Mihax209/mispecky/media/mispecky box 2.jpeg

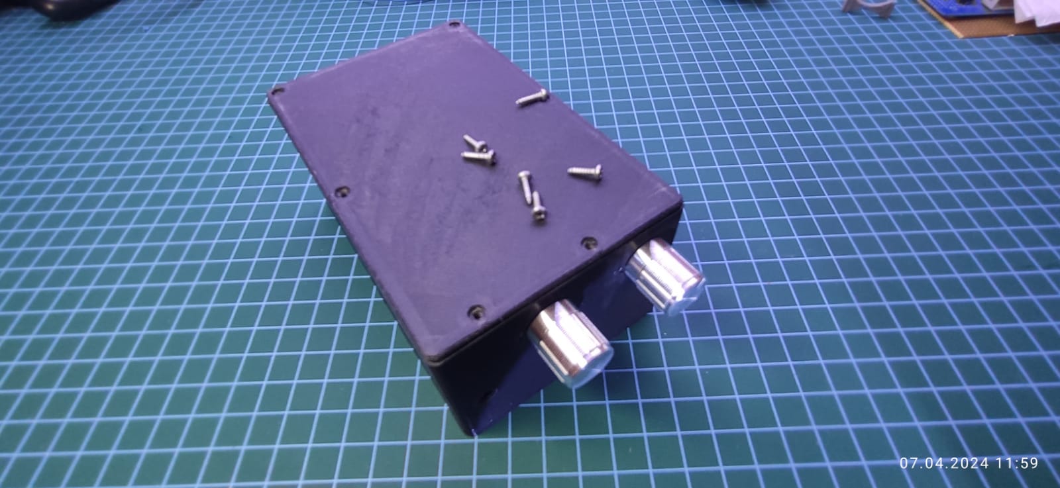
media/mispecky box 2.jpeg
