Mihax209/mispecky/src/models/Meshify C TG/partial stl/Meshify FULLcache_psu_001.stl

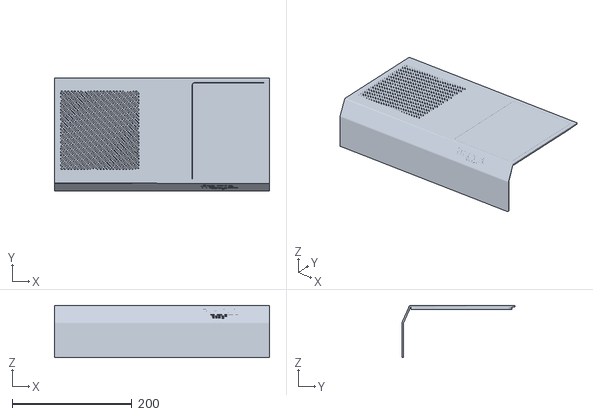
[picture p21: CAD file, 2024-03-31]
src/models/Meshify C TG/partial stl/Meshify FULLcache_psu_001.stl
359.7 x 189.7 x 87.1
