Mihax209/mispecky/models/Meshify C TG/full stl/Meshify BodyPieds_tour.stl

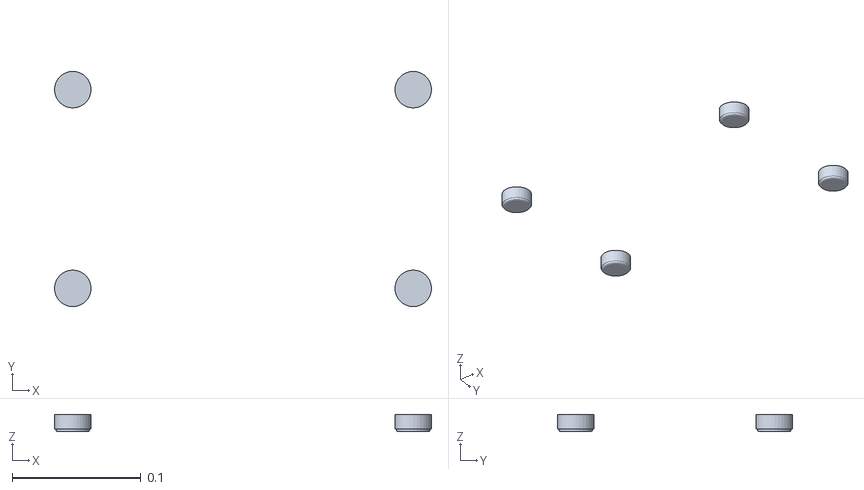
[picture p22: CAD file, 2024-03-31]
models/Meshify C TG/full stl/Meshify BodyPieds_tour.stl
0.293 x 0.183 x 0.0134
