Mihax209/mispecky/src/models/Meshify C TG/full stl/Meshify BodySupport_motherboard_002.stl

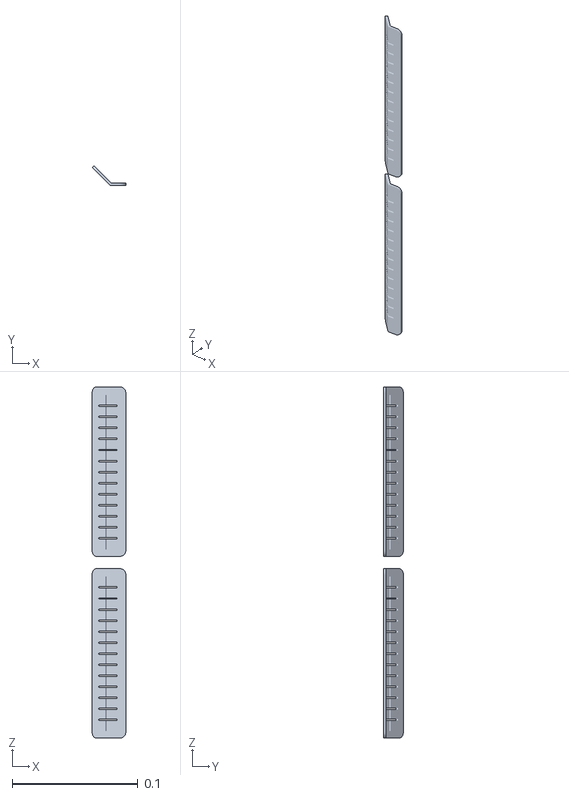
[picture p23: CAD file, 2024-03-31]
src/models/Meshify C TG/full stl/Meshify BodySupport_motherboard_002.stl
0.0268 x 0.0157 x 0.279
