Mihax209/mispecky/models/Meshify C TG/full stl/Meshify BodyHaut.stl

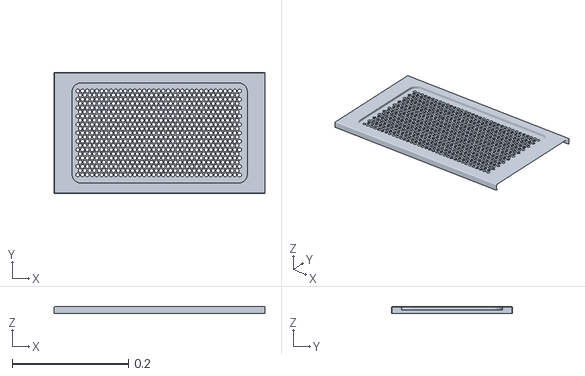
[picture p24: CAD file, 2024-03-31]
models/Meshify C TG/full stl/Meshify BodyHaut.stl
0.363 x 0.208 x 0.0118
