Mihax209/mispecky/src/models/Meshify C TG/full stl/Meshify Bodycaoutchouc_vitre_002.stl

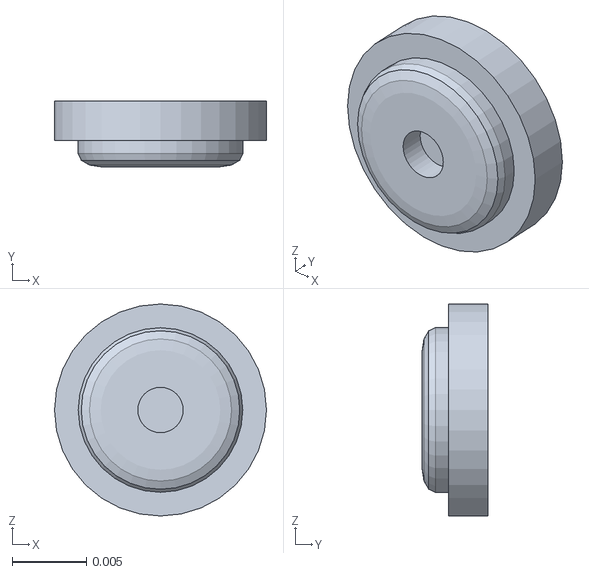
[picture p25: CAD file, 2024-03-31]
src/models/Meshify C TG/full stl/Meshify Bodycaoutchouc_vitre_002.stl
0.0143 x 0.00442 x 0.0143
