Mihax209/mispecky/models/Meshify C TG/full stl/Meshify Bodygrille_sup.stl

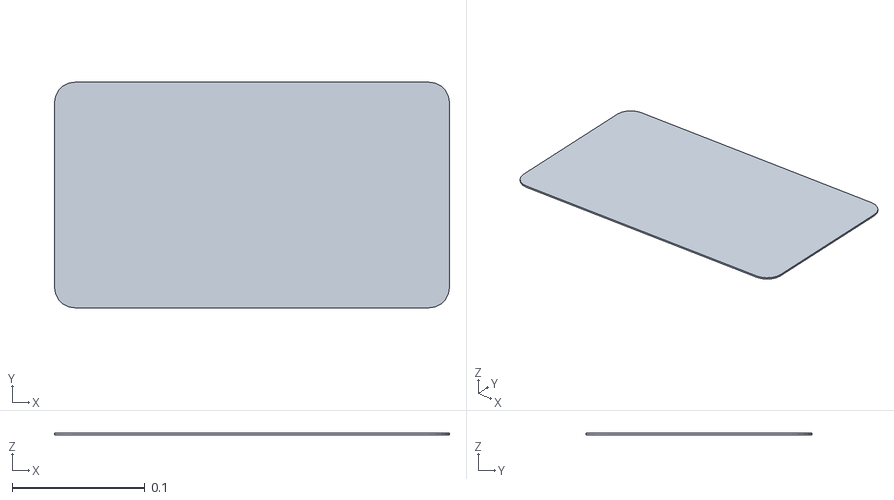
[picture p26: CAD file, 2024-03-31]
models/Meshify C TG/full stl/Meshify Bodygrille_sup.stl
0.298 x 0.17 x 0.00142
