Mihax209/mispecky/models/Meshify C TG/full stl/Meshify BodyLogo_front.stl

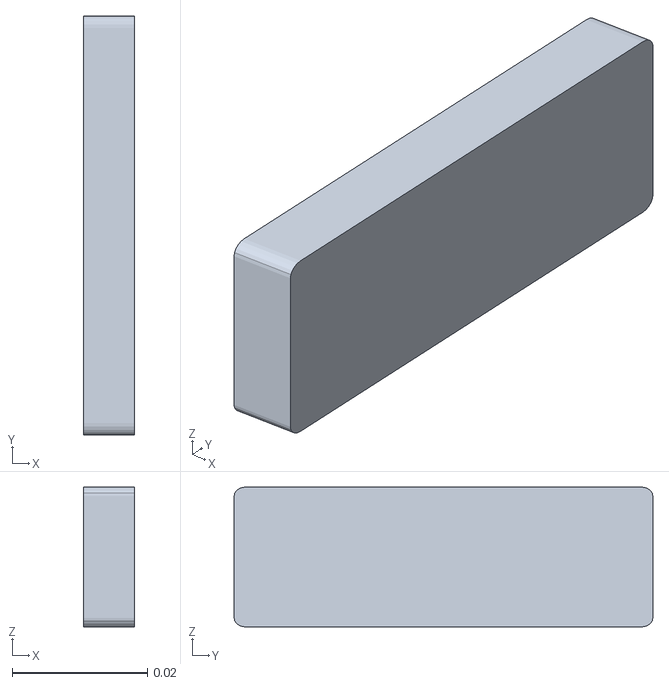
[picture p27: CAD file, 2024-03-31]
models/Meshify C TG/full stl/Meshify BodyLogo_front.stl
0.00752 x 0.0619 x 0.0207
