Mihax209/mispecky/src/models/Meshify C TG/full stl/Meshify Bodycache_psu_001.stl

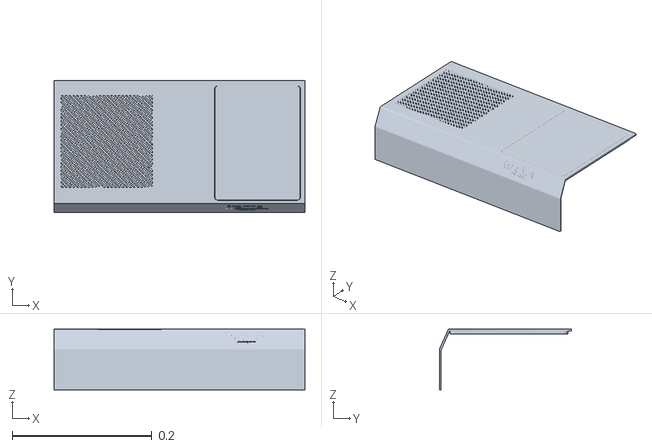
[picture p28: CAD file, 2024-03-31]
src/models/Meshify C TG/full stl/Meshify Bodycache_psu_001.stl
0.36 x 0.19 x 0.0871
