Mihax209/mispecky/models/Meshify C TG/full stl/Meshify BodyBas.stl

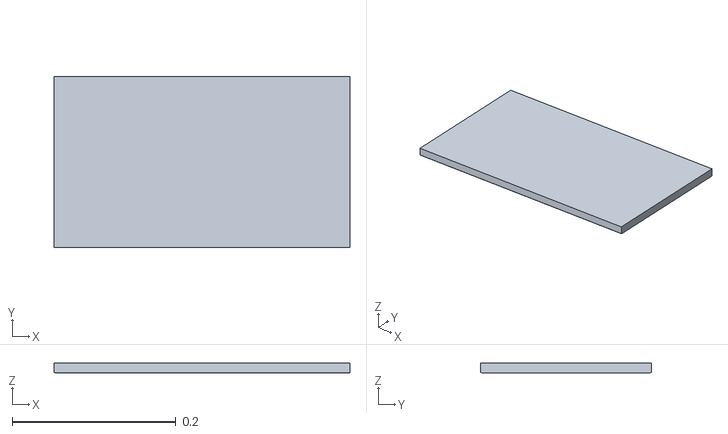
[picture p29: CAD file, 2024-03-31]
models/Meshify C TG/full stl/Meshify BodyBas.stl
0.361 x 0.208 x 0.0117
