Mihax209/mispecky/src/models/Meshify C TG/full stl/Meshify Bodyslot_plates.stl

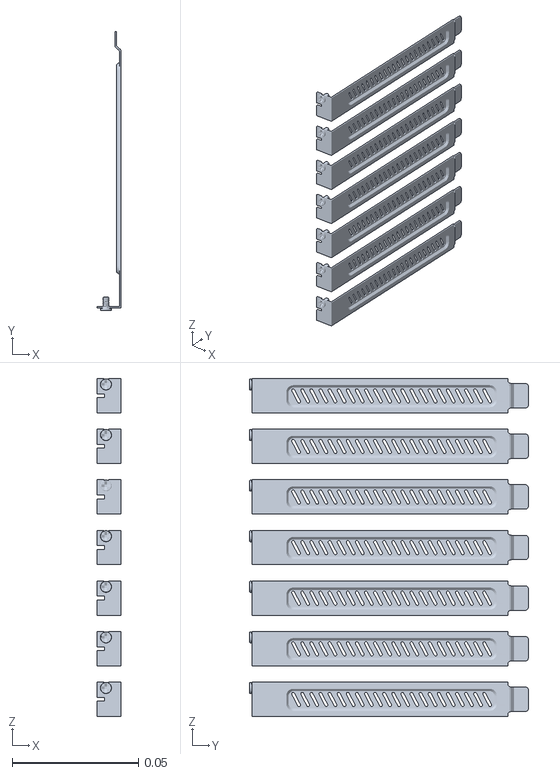
[picture p30: CAD file, 2024-03-31]
src/models/Meshify C TG/full stl/Meshify Bodyslot_plates.stl
0.00951 x 0.11 x 0.134
