Mihax209/mispecky/src/models/Meshify C TG/full stl/Meshify Bodyvis_TG.stl

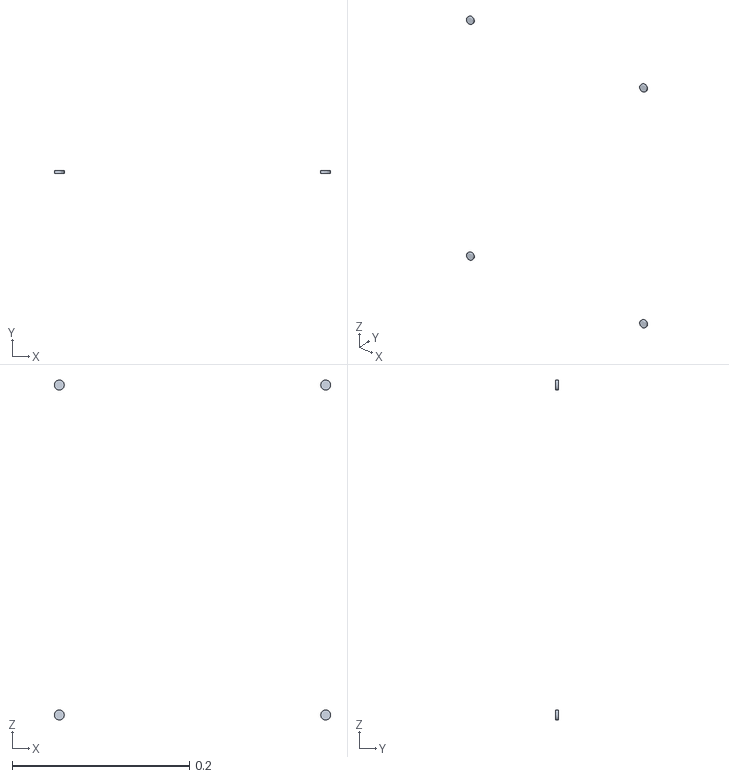
[picture p31: CAD file, 2024-03-31]
src/models/Meshify C TG/full stl/Meshify Bodyvis_TG.stl
0.312 x 0.00378 x 0.384
