Mihax209/mispecky/models/Meshify C TG/full stl/Meshify BodyFront_panel_002.stl

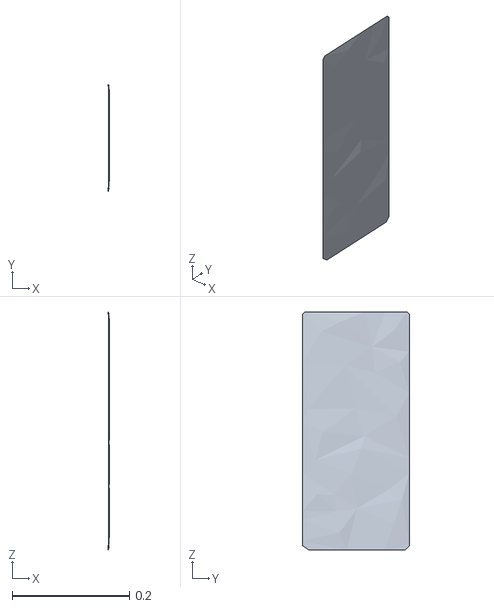
[picture p32: CAD file, 2024-03-31]
models/Meshify C TG/full stl/Meshify BodyFront_panel_002.stl
0.00219 x 0.183 x 0.407
