Mihax209/mispecky/src/models/Meshify C TG/full stl/Meshify BodyGrande_vis_002.stl

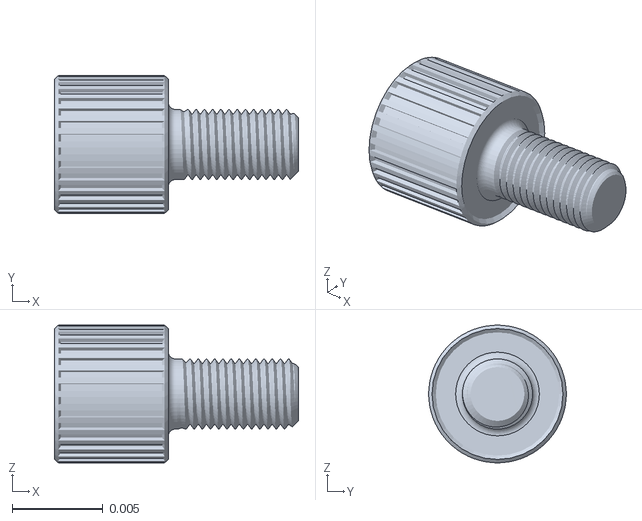
[picture p33: CAD file, 2024-03-31]
src/models/Meshify C TG/full stl/Meshify BodyGrande_vis_002.stl
0.0134 x 0.00756 x 0.00756
