Mihax209/mispecky/models/Meshify C TG/full stl/Meshify Bodychassis_vitre.stl

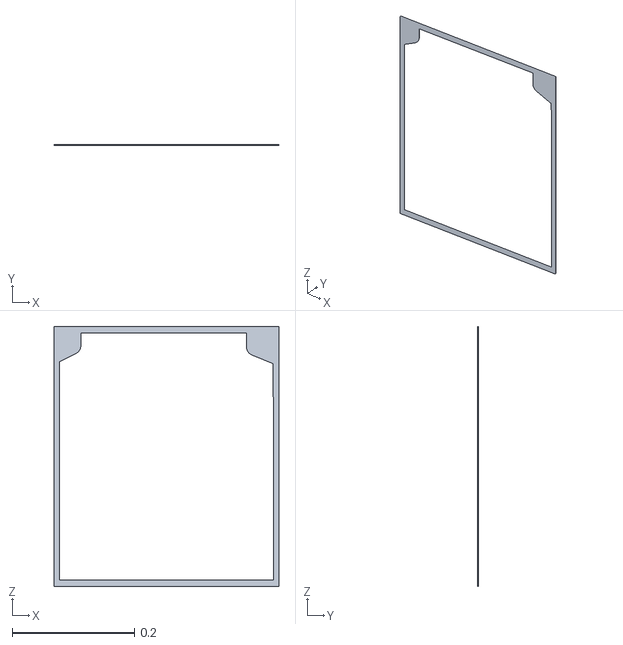
[picture p34: CAD file, 2024-03-31]
models/Meshify C TG/full stl/Meshify Bodychassis_vitre.stl
0.367 x 0.00199 x 0.425
