Mihax209/mispecky/models/Meshify C TG/full stl/Meshify BodyFront_panel_001.stl

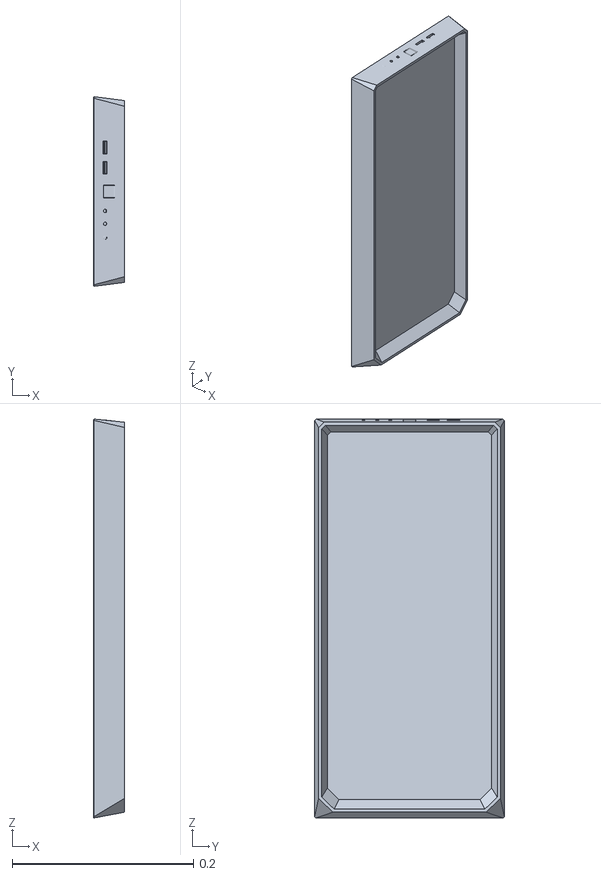
[picture p35: CAD file, 2024-03-31]
models/Meshify C TG/full stl/Meshify BodyFront_panel_001.stl
0.0342 x 0.209 x 0.44
