Mihax209/mispecky/models/Meshify C TG/full stl/Meshify Bodycaoutchouc_vitre.stl

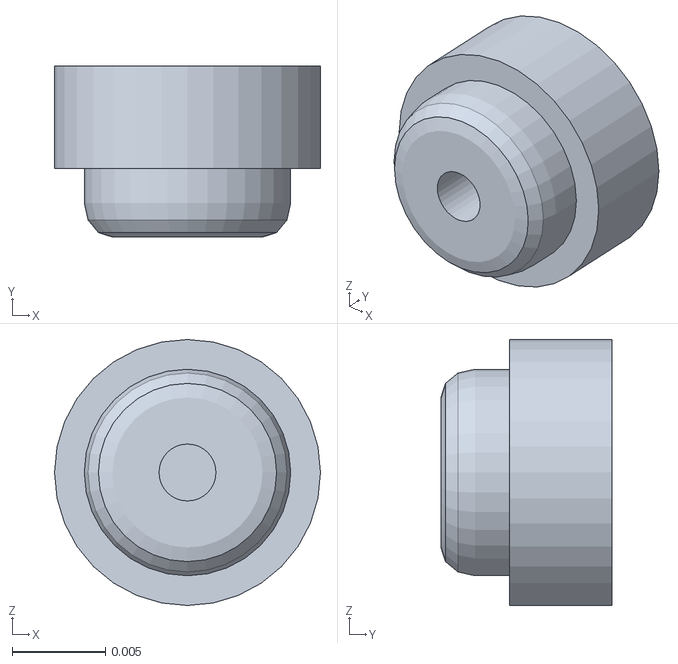
[picture p36: CAD file, 2024-03-31]
models/Meshify C TG/full stl/Meshify Bodycaoutchouc_vitre.stl
0.0143 x 0.00919 x 0.0143
