Mihax209/mispecky/models/Meshify C TG/full stl/Meshify BodyArriere_001.stl

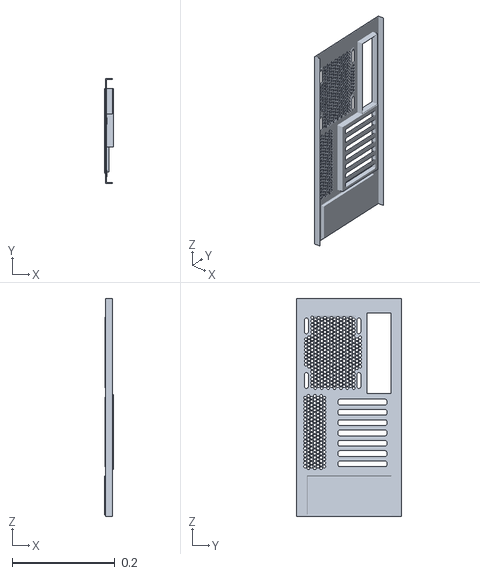
[picture p37: CAD file, 2024-03-31]
models/Meshify C TG/full stl/Meshify BodyArriere_001.stl
0.0167 x 0.204 x 0.425
