Mihax209/mispecky/src/models/Meshify C TG/full stl/Meshify Bodyvitre.stl

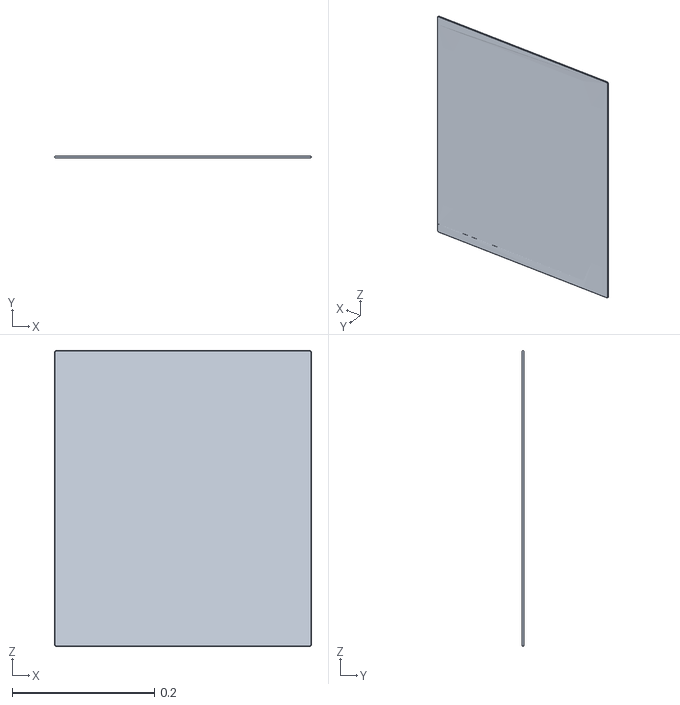
[picture p38: CAD file, 2024-03-31]
src/models/Meshify C TG/full stl/Meshify Bodyvitre.stl
0.362 x 0.0025 x 0.416
