Mihax209/mispecky/models/Meshify C TG/full stl/Meshify BodyFond.stl

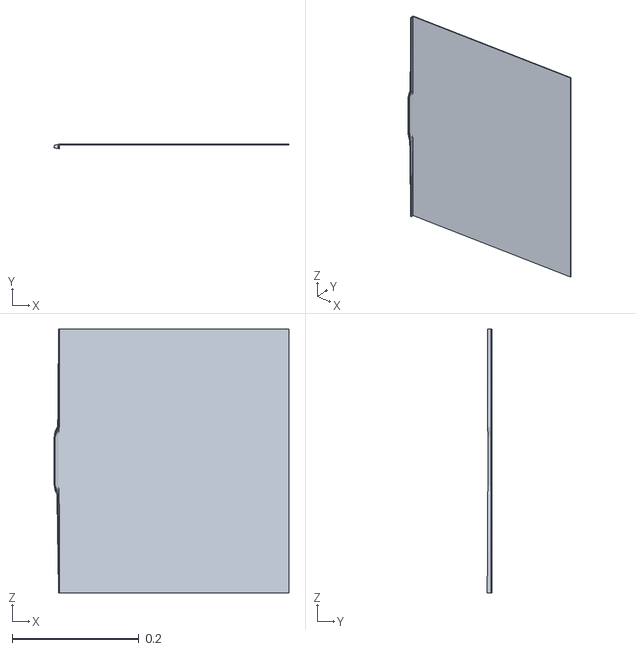
[picture p39: CAD file, 2024-03-31]
models/Meshify C TG/full stl/Meshify BodyFond.stl
0.37 x 0.00735 x 0.417
