Mihax209/mispecky/src/models/Meshify C TG/full stl/Meshify BodyCurve.stl

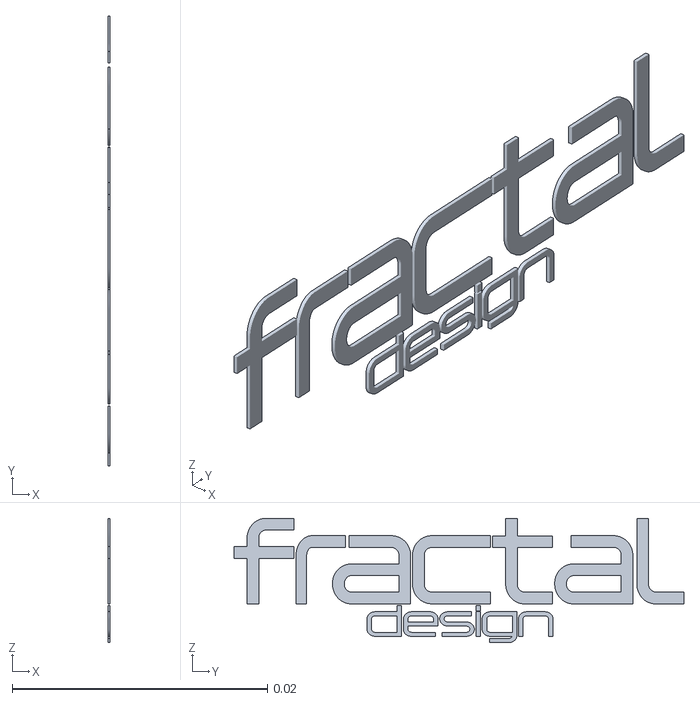
[picture p40: CAD file, 2024-03-31]
src/models/Meshify C TG/full stl/Meshify BodyCurve.stl
0.000195 x 0.0352 x 0.00974
