Mihax209/mispecky/models/Meshify C TG/full stl/Meshify BodySupport_motherboard.stl

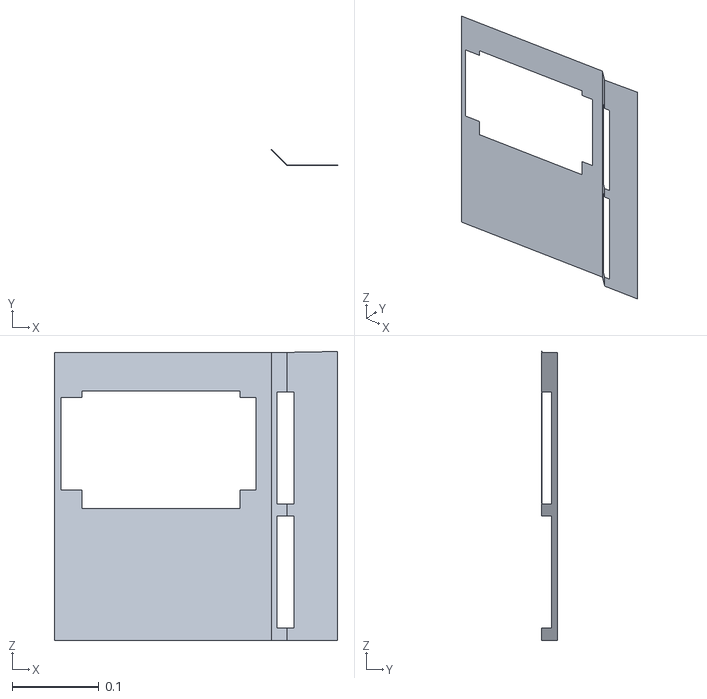
[picture p41: CAD file, 2024-03-31]
models/Meshify C TG/full stl/Meshify BodySupport_motherboard.stl
0.325 x 0.0179 x 0.332
