Mihax209/mispecky/src/led.cpp

#include <Arduino.h>
#include <FastLED.h>

#include <common.h>
#include <spectrum.h>
#include <led.h>

#define SMOOTHNESS_MIN  (1-0.5)
#define SMOOTHNESS_MAX  (1-0.98)

/* PRIVATE FUNCTIONS */
int getColumnHeight(int column);
void printColumnHeight(int col, int height);
void setLMHColorMatrix(CRGB low_color, CRGB mid_color, CRGB high_color);
void verticalGradientColor();
void horizontalGradientColor();
float mapToFloat(int value, int in_min, int in_max, float out_min, float out_max);


/* GLOBAL VARIABLES */
float prev_column_values[COLUMNS] = {0};
bool lit_matrix[COLUMNS][ROWS];

struct CRGB color_matrix[COLUMNS][ROWS];
struct CRGB fastLED_matrix[(COLUMNS*ROWS) - (2*AMOUNT_TRIMMED)];

static int g_curr_brightness = DEFAULT_BRIGHT;


void LED_init()
{
    FastLED.addLeds<WS2812B, DATA_PIN, GRB>(fastLED_matrix, LENOF(fastLED_matrix));
    FastLED.setMaxPowerInVoltsAndMilliamps(5, 2000);
    LED_updateBrightness(DEFAULT_BRIGHT);
}


void LED_updateBrightness(int brightness)
{
    g_curr_brightness = brightness;
    FastLED.setBrightness(brightness);
    DEBUG_DO(Serial.print("Brightness updated to: "));
    DEBUG_DO(Serial.println(brightness));
}


void LED_updateLEDMatrix()
{
    for (int col = 0; col < COLUMNS; ++col) {
        unsigned int height = min(getColumnHeight(col), ROWS);
        /* light up EQ band */
        for (unsigned int row = 0; row < ROWS; ++row) {
            lit_matrix[col][row] = (row < height);
        }

        DEBUG_DO(printColumnHeight(col, height));
    }

    for (int col = 0; col < COLUMNS; ++col) {
        for (int row = 0; row < ROWS; ++row) {
            int flat_index = (col * ROWS) + row - AMOUNT_TRIMMED;

            if (flat_index >= 0) {
                fastLED_matrix[flat_index] =
                    lit_matrix[col][row] ? color_matrix[col][row] : CRGB::Black;
            }
        }
    }

    FastLED.show();
}

/* NOTE: THIS WILL NEED TO BE CHANGED ACCRODING TO AMOUNT OF COLUMNS */
/* This is a 14 -> 12 band convertor */
int getColumnHeight(int column) {
    float current, previous, value = 0;
    float alpha = mapToFloat(analogRead(SMOOTH_PIN), 0, 1023, SMOOTHNESS_MIN, SMOOTHNESS_MAX);

    previous = prev_column_values[column];
    current = SPECTRUM_getBandValue(column + 1);
    if (column == 0) {
        // Bass max value with truncated band
        current = max(current, SPECTRUM_getBandValue(0));
    }
    current /= EQ_DELTA;

    value = (current * alpha) + (previous * (1.0-alpha));
    prev_column_values[column] = value;

    return min(ROWS, (int)value);
}


void printColumnHeight(int col, int height)
{
    Serial.print("Column height: "); Serial.print(height);
}


void LED_setColorMatrix(enum color_effect effect)
{
    switch (effect) {
    case DEFAULT_COLOR:
        setLMHColorMatrix(CRGB::Cyan, CRGB::Yellow, CRGB::Magenta);
        break;
    case DEFAULT2_COLOR:
        setLMHColorMatrix(CRGB(0x9f0092), CRGB(0x149106), CRGB(0x028f8a));
        break;
    case CALM_COLOR:
        setLMHColorMatrix(CRGB(0x4a2003), CRGB(0x082f0b), CRGB(0x2d0a22));
        break;
    case VERTICAL_GRADIENT:
        verticalGradientColor();
        break;
    case HORITZONTAL_GRADIENT:
        horizontalGradientColor();
        break;
    default:
        DEBUG_DO(Serial.print("ERROR: got to updateColorMatrix with effect num: "));
        DEBUG_DO(Serial.println(effect));

        setLMHColorMatrix(CRGB::Cyan, CRGB::Yellow, CRGB::Magenta);
        break;
    }
}

void LED_setCustomColorMatrix(unsigned long low_color, unsigned long mid_color, unsigned long high_color)
{
    setLMHColorMatrix((CRGB)low_color, (CRGB)mid_color, (CRGB)high_color);
}

void setLMHColorMatrix(CRGB low_color, CRGB mid_color, CRGB high_color)
{
    for (int col = 0; col < COLUMNS; ++col) {
        for (int row = 0; row < ROWS; ++row) {
            color_matrix[col][row] = 
                (row < 11) ? low_color : (row < 18 ? mid_color : high_color);
        }
    }
}

void verticalGradientColor()
{
    int start_hue = 235;
    int end_hue = 5;

    int curr_hue = start_hue;
    for (int row = 0; row < ROWS; ++row) {
        for (int col = 0; col < COLUMNS; ++col) {
            color_matrix[col][row] = CHSV((uint8_t)curr_hue, 255, 255);
        }

        curr_hue += (end_hue - start_hue) / ROWS;
    }
}

void horizontalGradientColor()
{
    int start_hue = 240;
    int end_hue = 0;

    int curr_hue = start_hue;
    for (int col = 0; col < COLUMNS; ++col) {
        for (int row = 0; row < ROWS; ++row) {
            color_matrix[col][row] = CHSV((uint8_t)curr_hue, 255, 255);
        }

        curr_hue += (end_hue - start_hue) / COLUMNS;
    }
}

float mapToFloat(int value, int in_min, int in_max, float out_min, float out_max) {
    return ((float)value - (float)in_min) * ((float)out_max - (float)out_min) / ((float)in_max - (float)in_min) + (float)out_min;
}
